Vitech-UA/SW_SWITCHED_LPF_BANK/MEDIA/3.6MHZ/3.6M.s21.jpeg

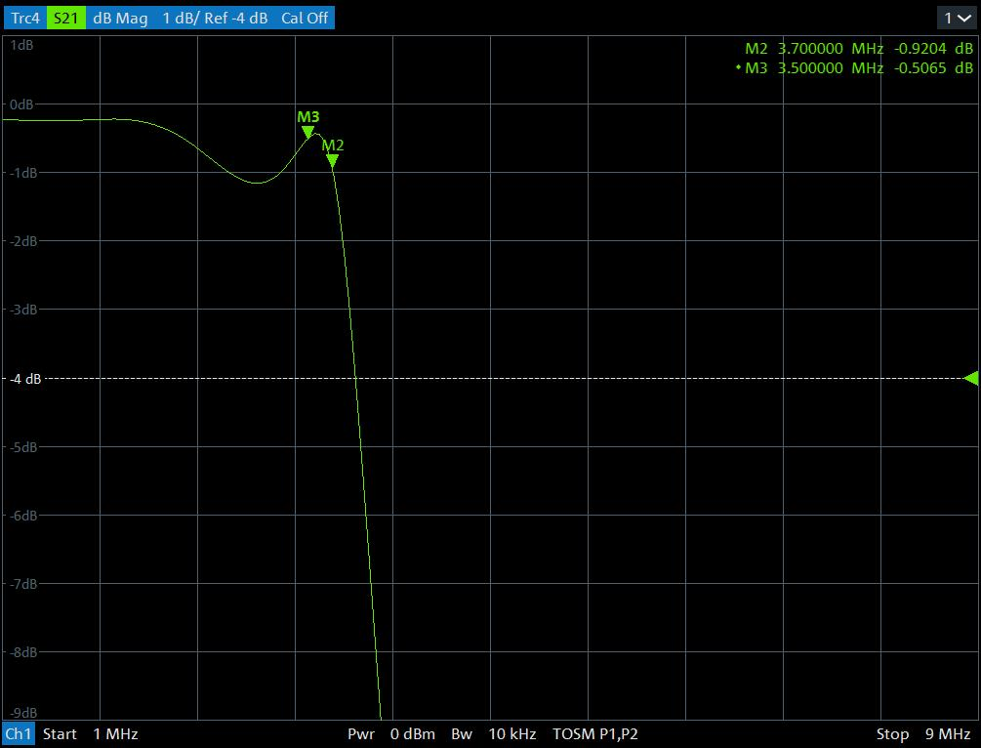
MEDIA/3.6MHZ/3.6M.s21.jpeg
