Vitech-UA/SW_SWITCHED_LPF_BANK/SRC/Розрахунок фільтра на 7,7МГц.jpg

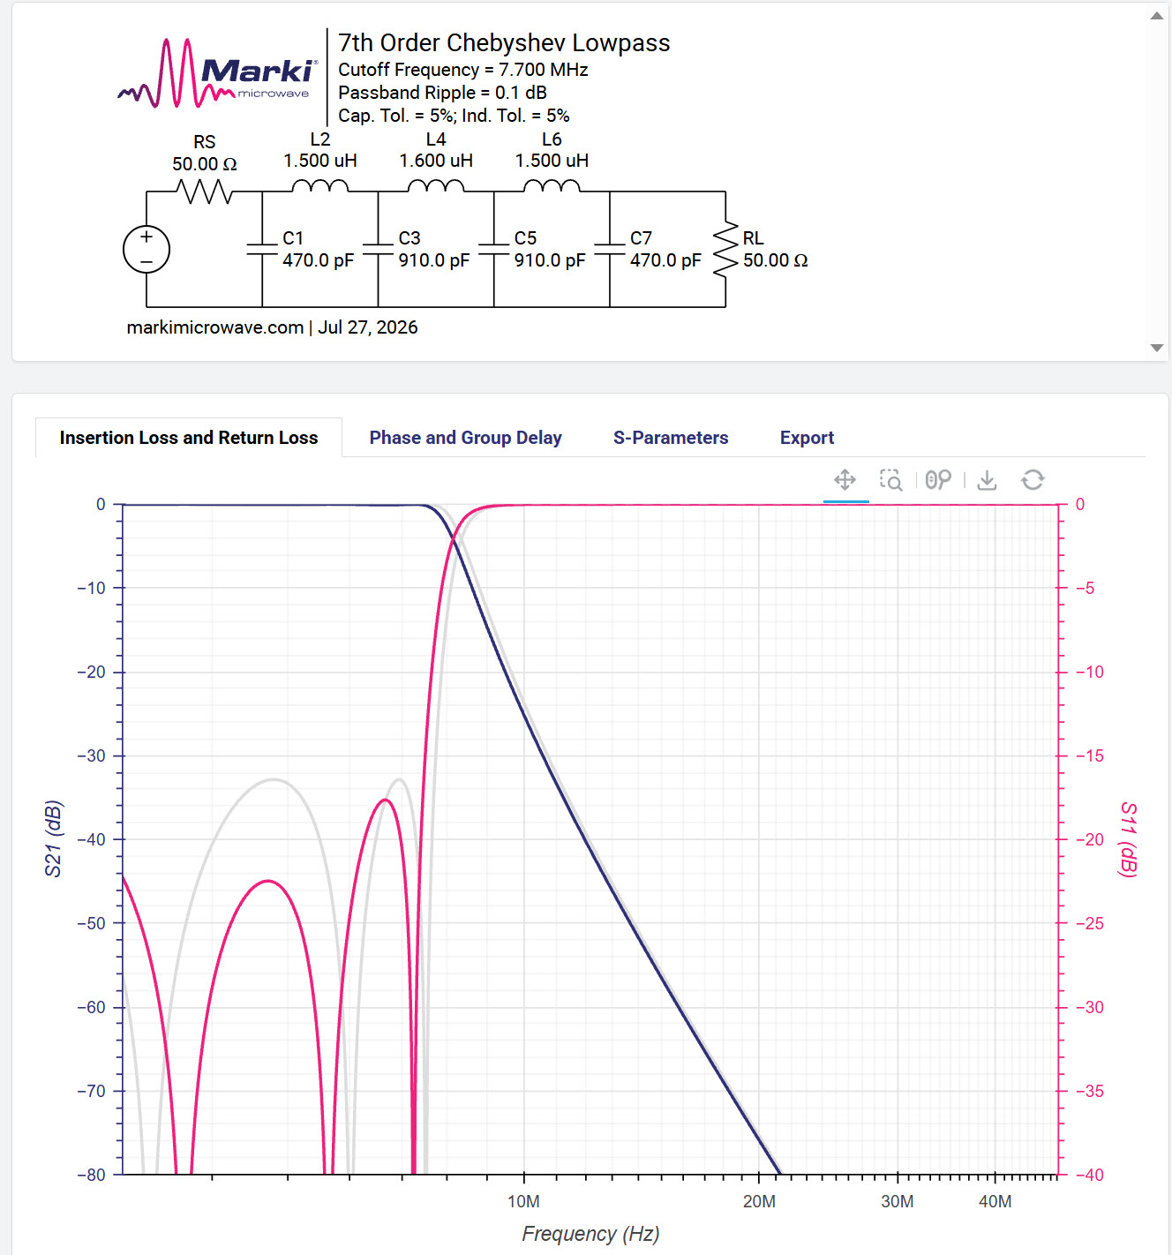
SRC/Розрахунок фільтра на 7,7МГц.jpg
